Musab-Hassan/aurora_keyboard/right_ergogen/output/outlines/2u_stabilizer.dxf

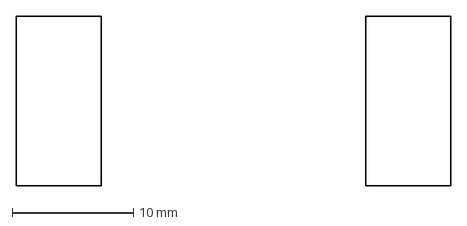
[picture p17: CAD file, 2024-10-24]
right_ergogen/output/outlines/2u_stabilizer.dxf
35.8 x 14.0 mm
