Musab-Hassan/aurora_keyboard/case/CAD/right_plate.SLDPRT

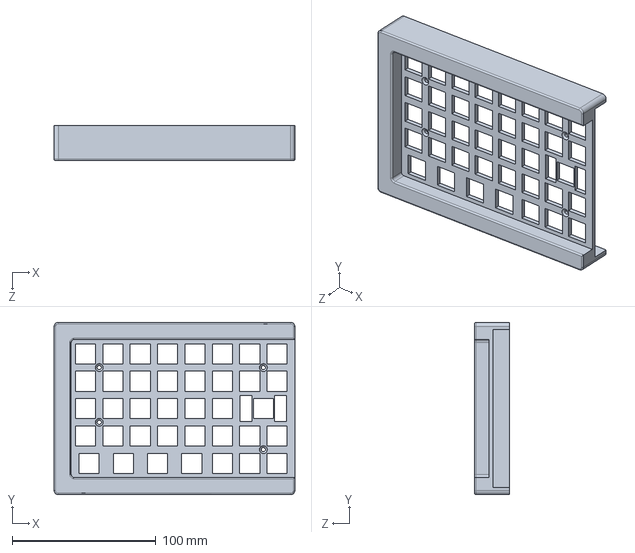
[picture p18: CAD file, 2025-01-29]
case/CAD/right_plate.SLDPRT
167.9 x 120.0 x 24.5 mm
