Musab-Hassan/aurora_keyboard/left_ergogen/output/outlines/keys_w_stabs.dxf

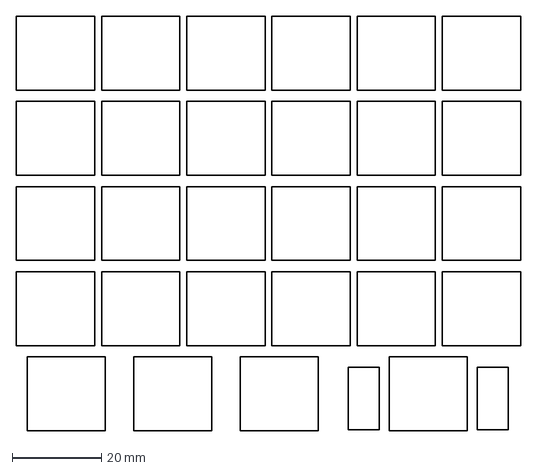
[picture p19: CAD file, 2024-10-24]
left_ergogen/output/outlines/keys_w_stabs.dxf
112.8 x 92.7 mm
