Musab-Hassan/aurora_keyboard/right_ergogen/output/outlines/raw.dxf

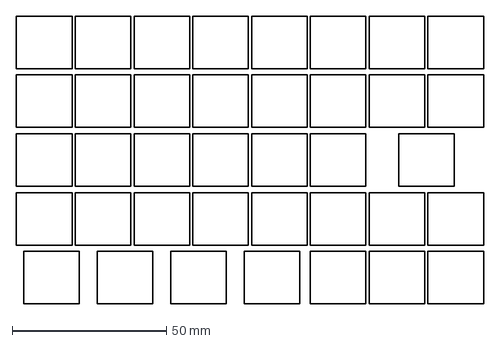
[picture p20: CAD file, 2024-10-24]
right_ergogen/output/outlines/raw.dxf
151.3 x 93.2 mm
