Musab-Hassan/aurora_keyboard/case/CAD/dongle.SLDPRT

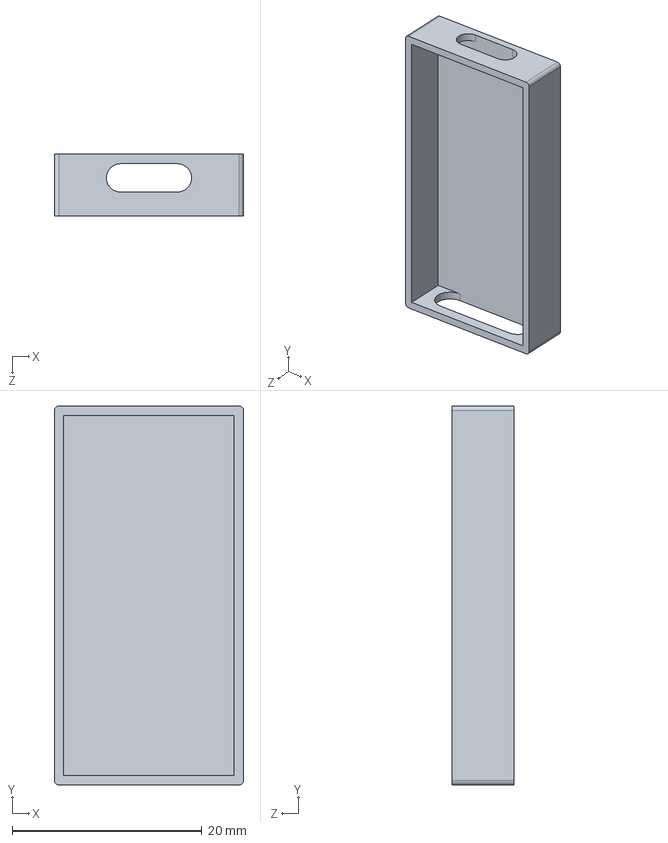
[picture p21: CAD file, 2025-01-29]
case/CAD/dongle.SLDPRT
20.0 x 40.0 x 6.50 mm
