Musab-Hassan/aurora_keyboard/left_ergogen/output/outlines/raw.dxf

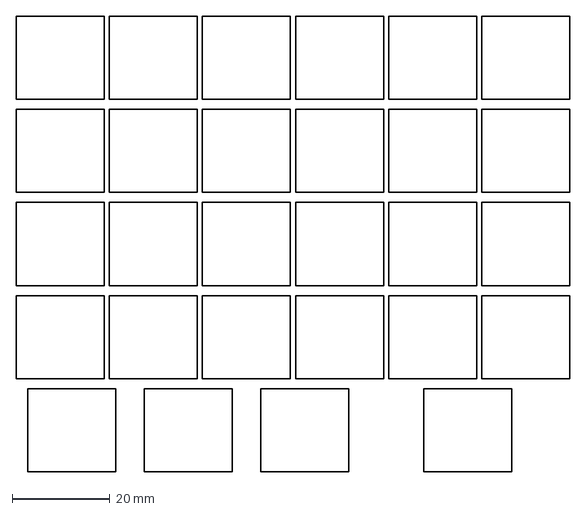
[picture p22: CAD file, 2024-10-24]
left_ergogen/output/outlines/raw.dxf
113.2 x 93.2 mm
