Musab-Hassan/aurora_keyboard/right_ergogen/output/outlines/keys.dxf

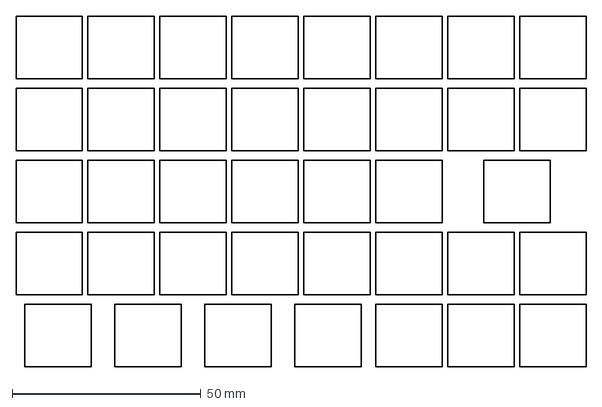
[picture p23: CAD file, 2024-10-24]
right_ergogen/output/outlines/keys.dxf
150.8 x 92.7 mm
