Musab-Hassan/aurora_keyboard/case/CAD/left_plate.SLDPRT

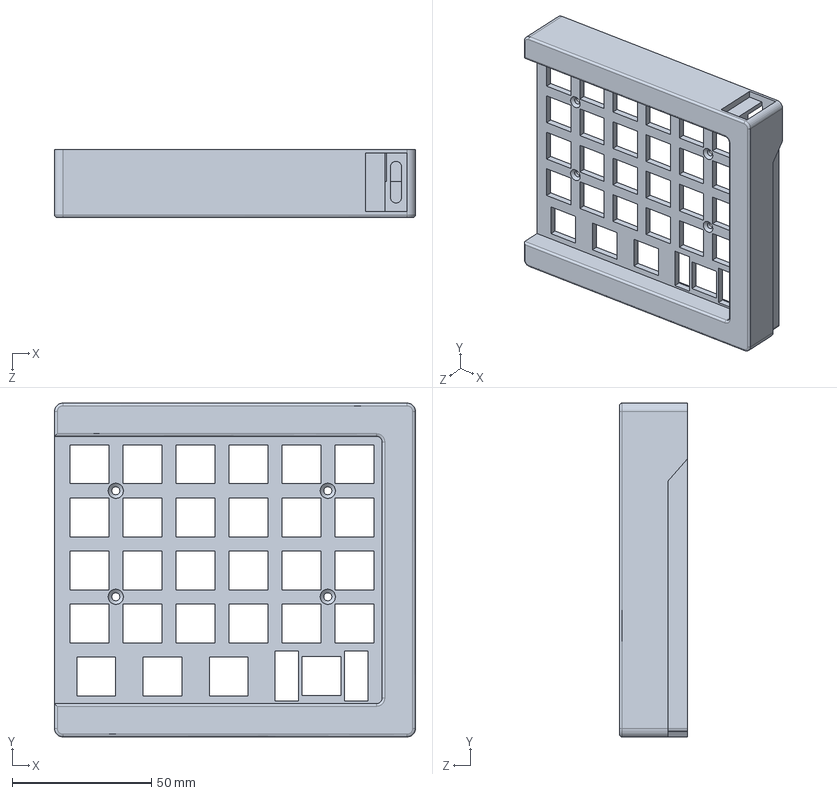
[picture p24: CAD file, 2025-01-29]
case/CAD/left_plate.SLDPRT
129.8 x 120.0 x 24.5 mm
