Musab-Hassan/aurora_keyboard/case/CAD/dongle_cover.SLDPRT

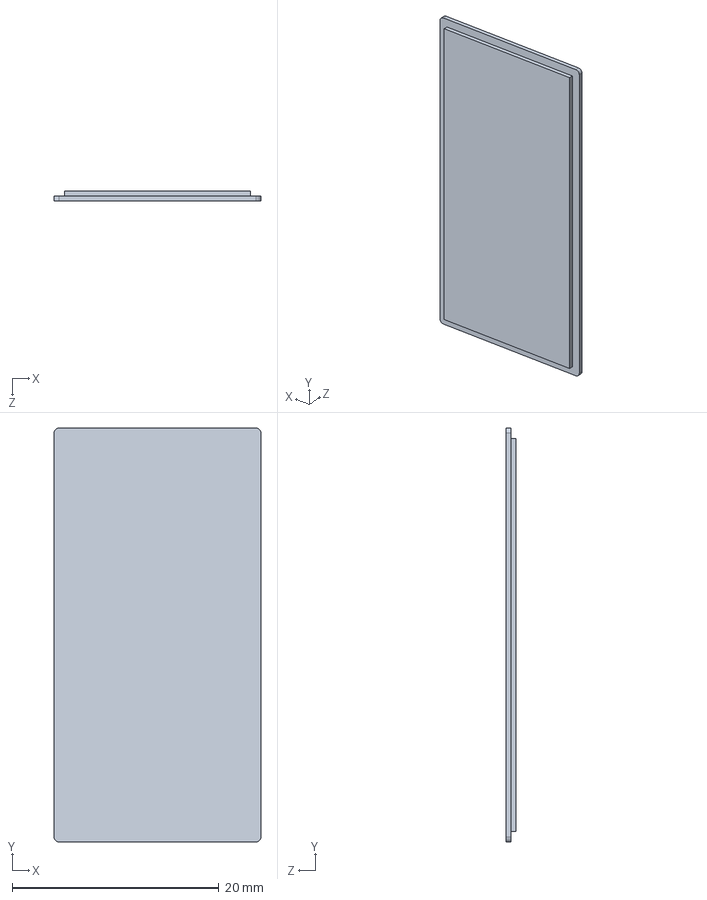
[picture p26: CAD file, 2025-01-29]
case/CAD/dongle_cover.SLDPRT
20.0 x 40.0 x 1.00 mm
