Musab-Hassan/aurora_keyboard/case/CAD/acrylic_shield.SLDPRT

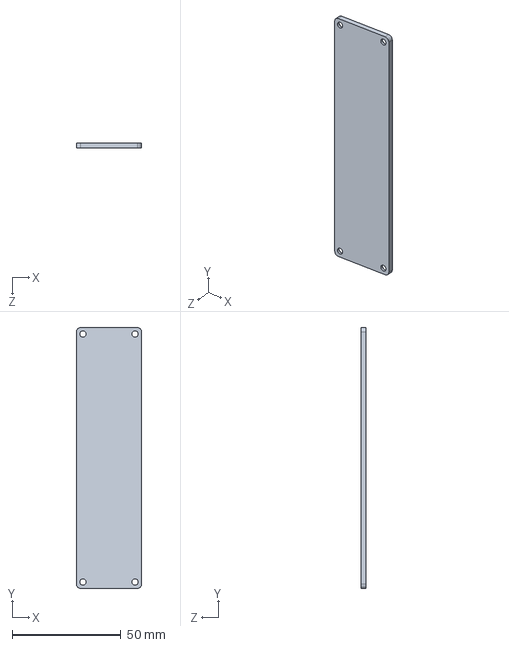
[picture p27: CAD file, 2025-01-29]
case/CAD/acrylic_shield.SLDPRT
30.0 x 120.0 x 2.50 mm
