Musab-Hassan/aurora_keyboard/case/CAD/left_base.SLDPRT

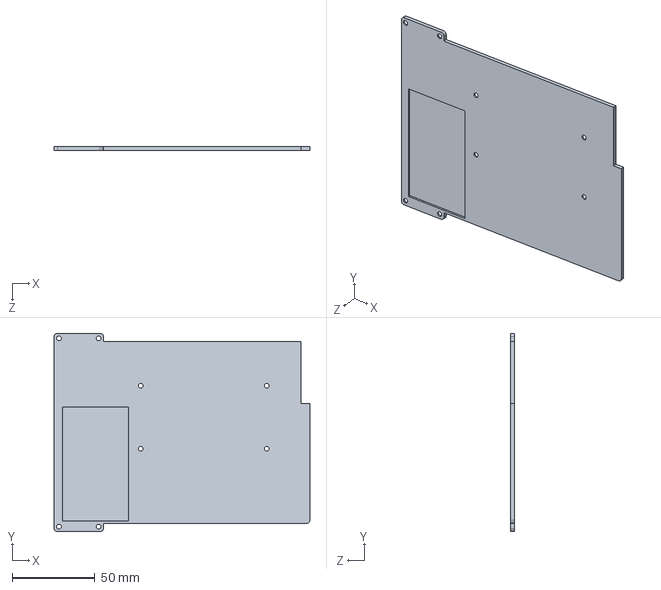
[picture p28: CAD file, 2025-01-29]
case/CAD/left_base.SLDPRT
155.0 x 120.0 x 2.20 mm
